RobertoPalozzo/esp32c3-case-design/Assessment_Files/200096469_RobertoPalozzo_ESP32Case_Final_Slicer.jpg

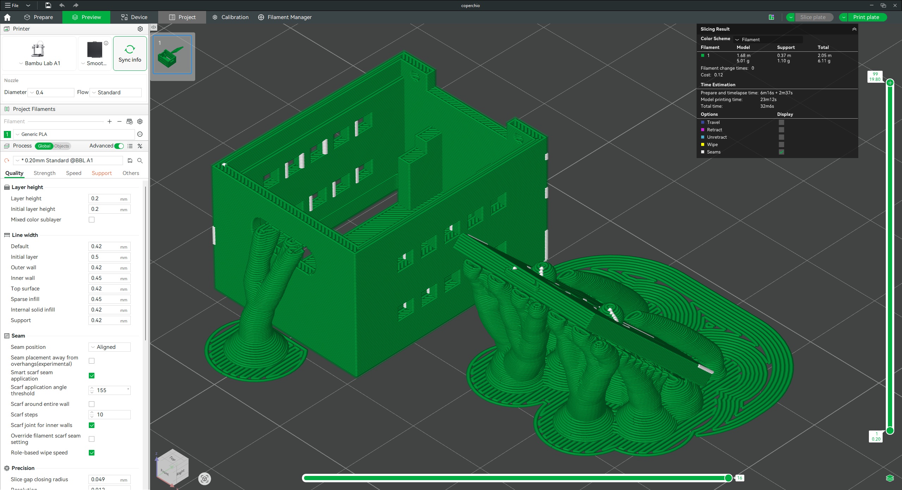
Assessment_Files/200096469_RobertoPalozzo_ESP32Case_Final_Slicer.jpg
