RobertoPalozzo/esp32c3-case-design/Assessment_Files/200096469_RobertoPalozzo_ESP32Case_Prototype1_Slicer.jpg

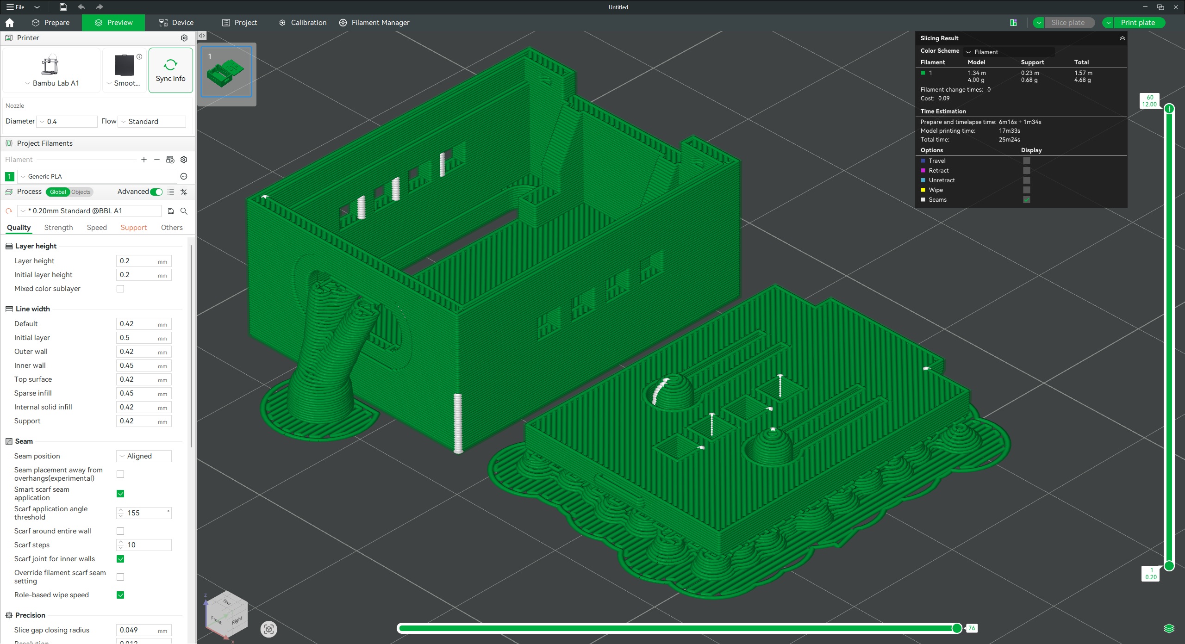
Assessment_Files/200096469_RobertoPalozzo_ESP32Case_Prototype1_Slicer.jpg
