RobertoPalozzo/esp32c3-case-design/images/alignment.jpg

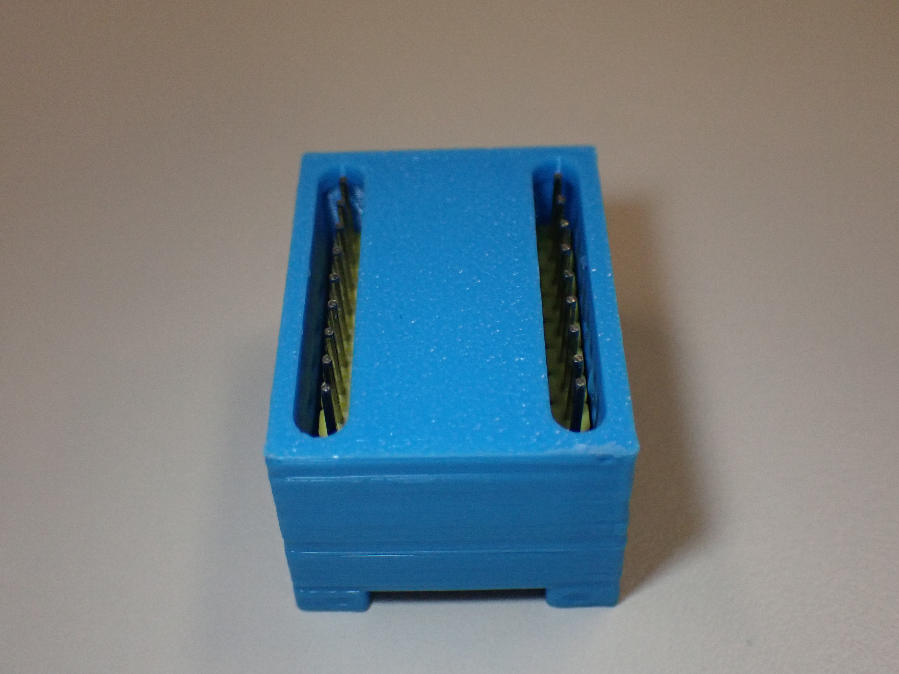
images/alignment.jpg
