RobertoPalozzo/esp32c3-case-design/images/board2.jpg

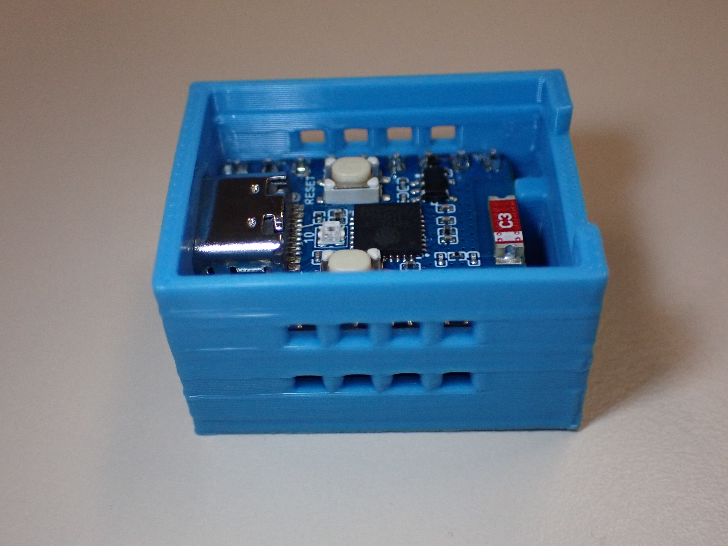
images/board2.jpg
