RobertoPalozzo/esp32c3-case-design/images/cable.jpg

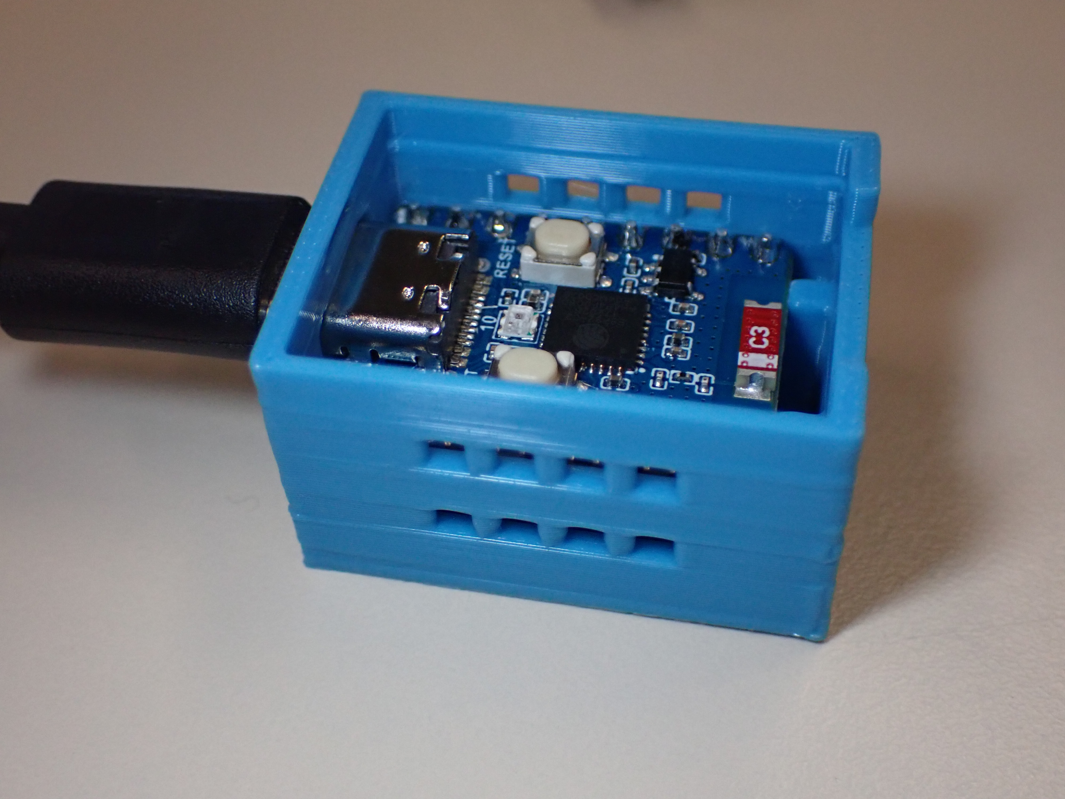
images/cable.jpg
