RobertoPalozzo/esp32c3-case-design/images/case1.jpg

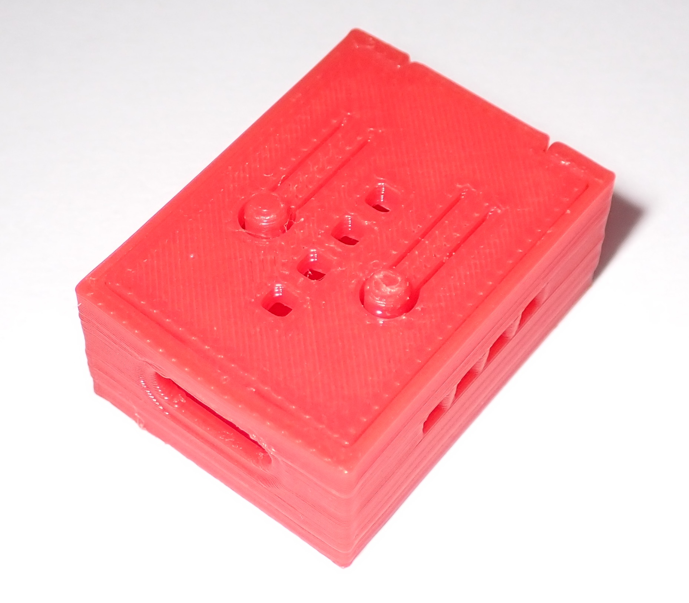
images/case1.jpg
