RobertoPalozzo/esp32c3-case-design/images/case2.jpg

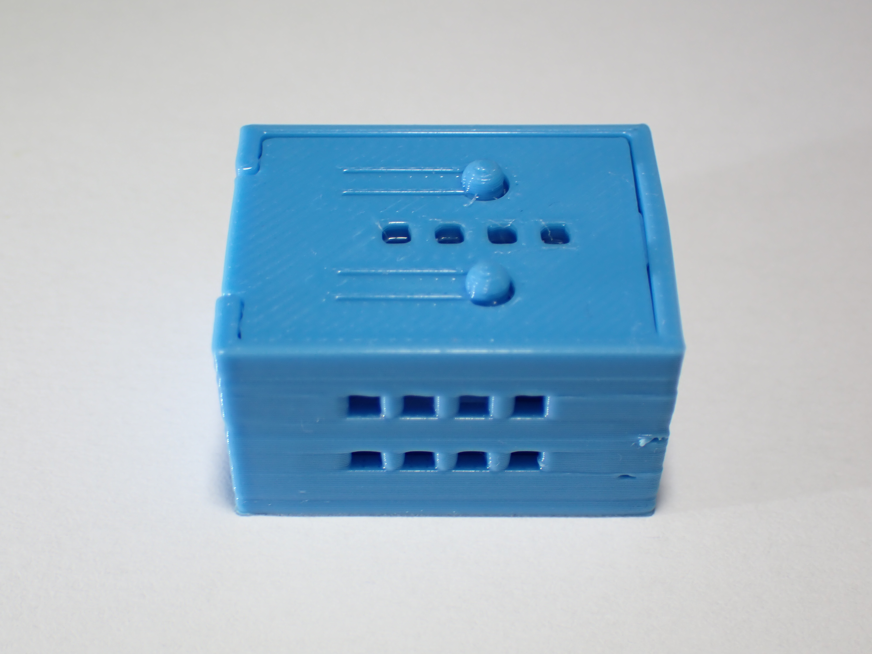
images/case2.jpg
