RobertoPalozzo/esp32c3-case-design/images/case3.jpg

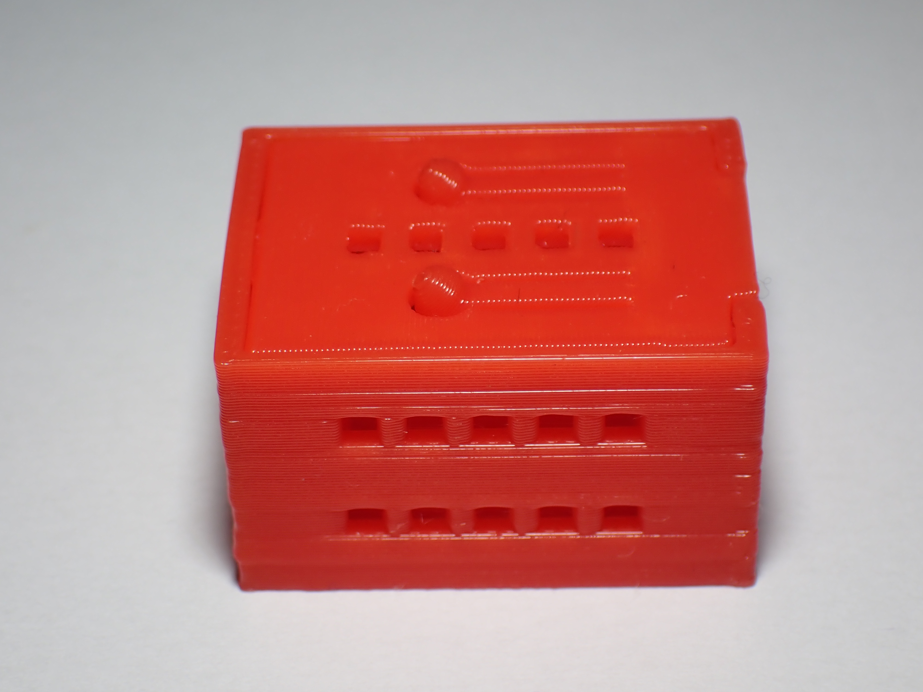
images/case3.jpg
