RobertoPalozzo/esp32c3-case-design/images/internal3.jpg

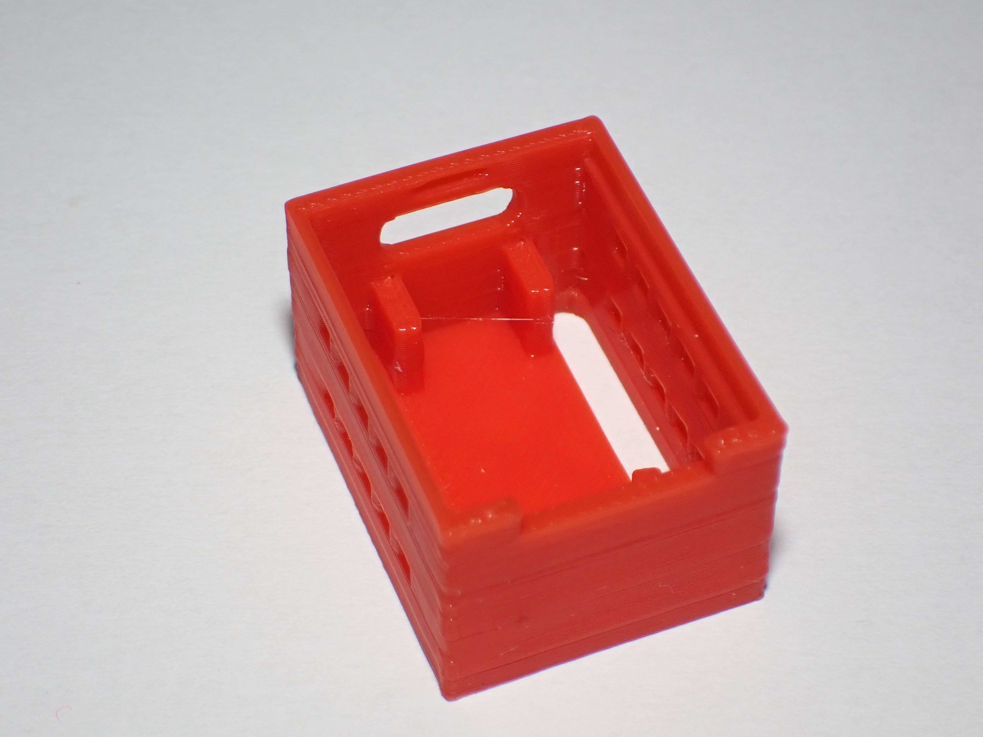
images/internal3.jpg
