RobertoPalozzo/esp32c3-case-design/images/Last_1_7.JPG

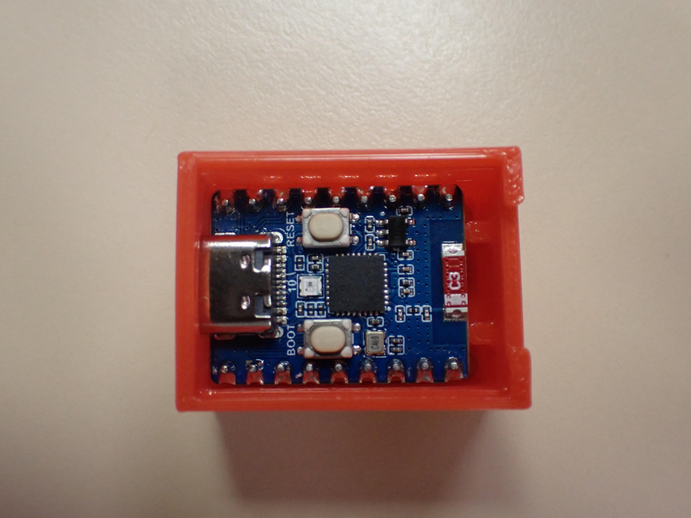
images/Last_1_7.JPG
