RobertoPalozzo/esp32c3-case-design/images/Last_1_9.JPG

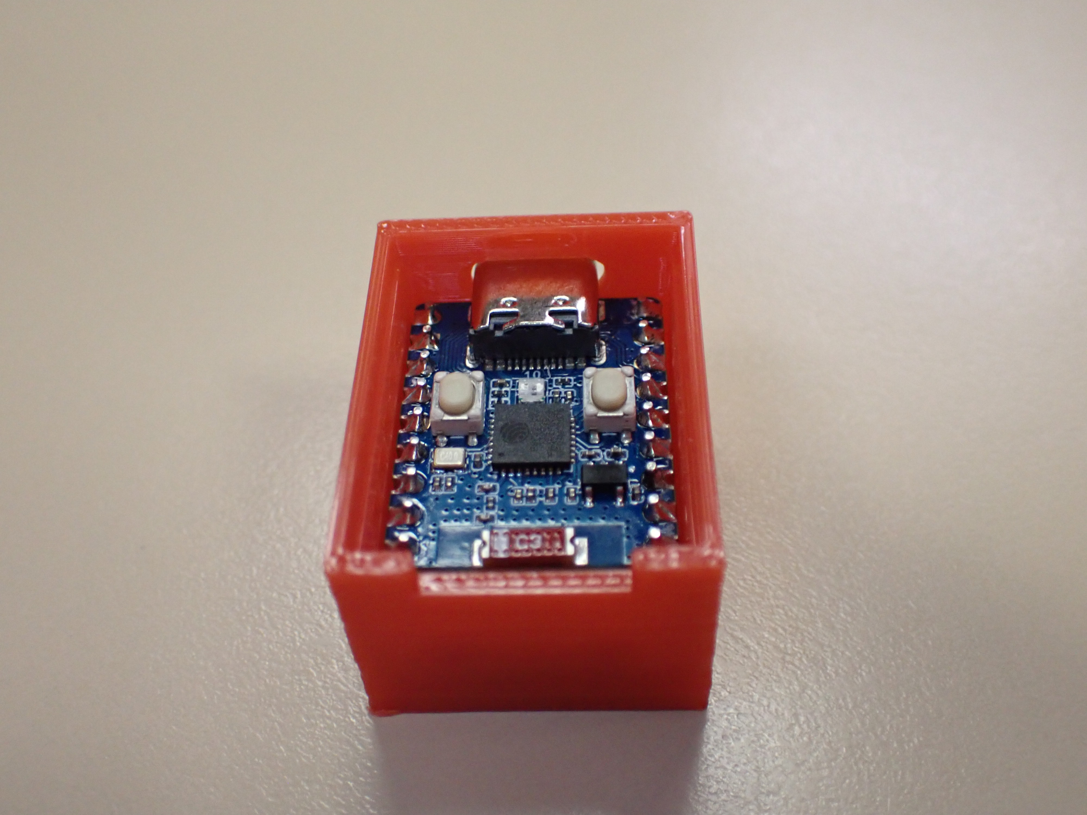
images/Last_1_9.JPG
