RobertoPalozzo/esp32c3-case-design/images/lid1.jpg

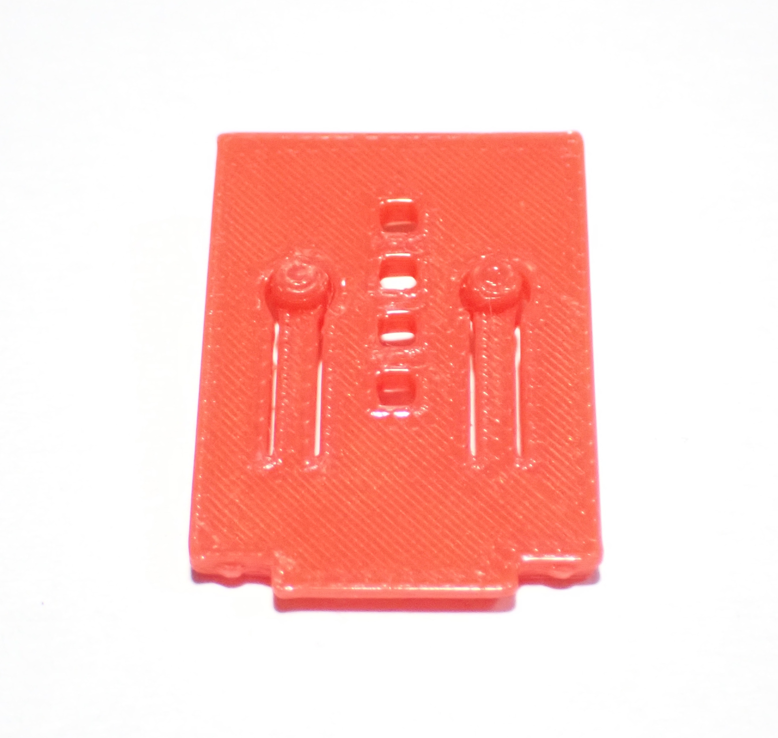
images/lid1.jpg
