RobertoPalozzo/esp32c3-case-design/images/lid3.jpg

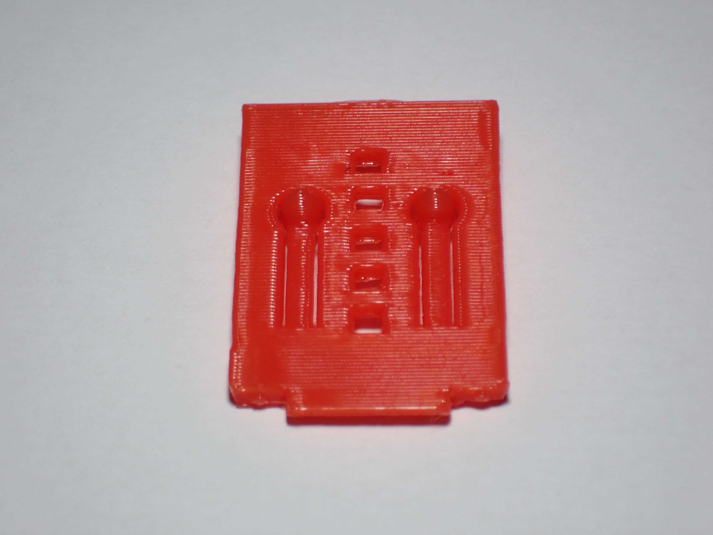
images/lid3.jpg
