RobertoPalozzo/esp32c3-case-design/images/long_pin.jpg

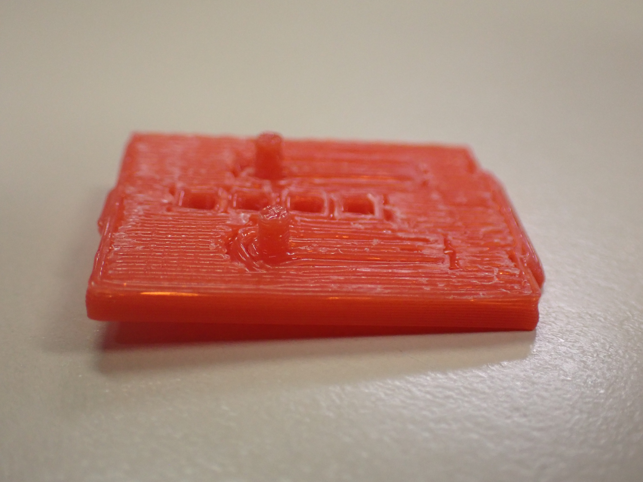
images/long_pin.jpg
