RobertoPalozzo/esp32c3-case-design/images/pins3.jpg

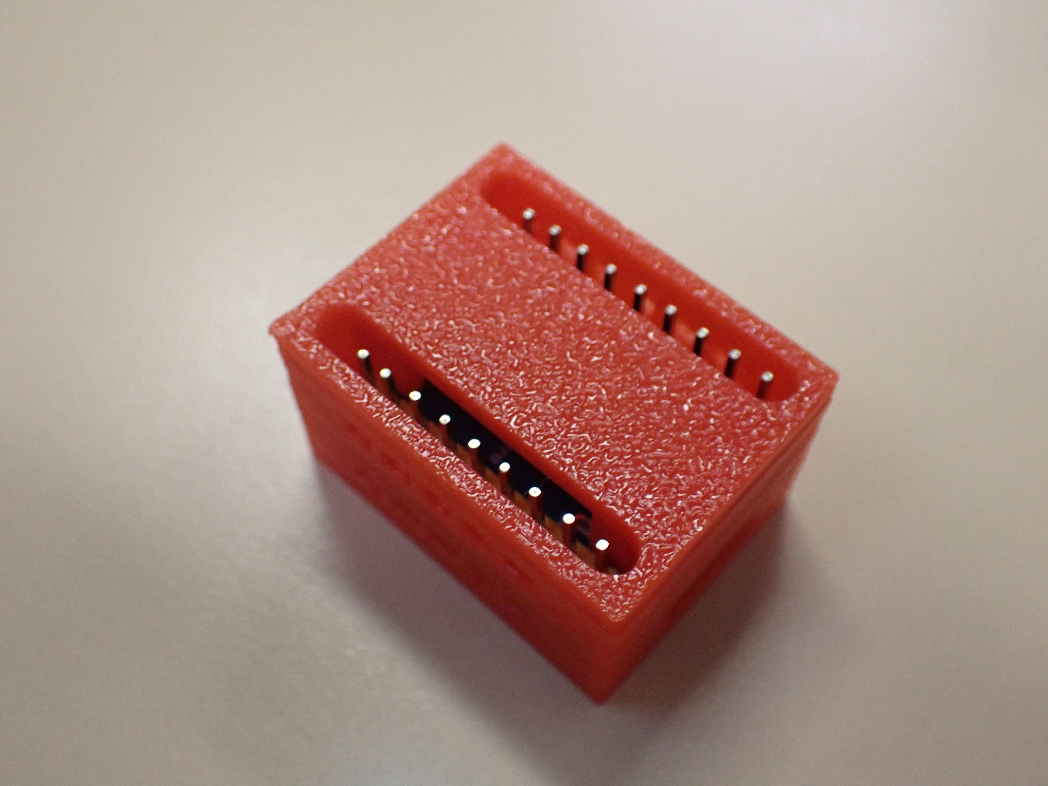
images/pins3.jpg
