RobertoPalozzo/esp32c3-case-design/images/prot1bot.jpg

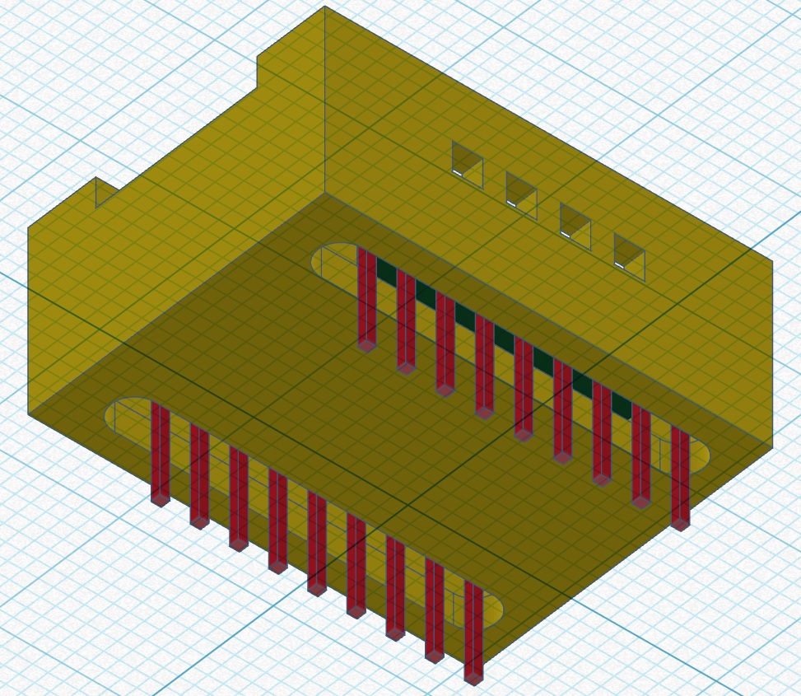
images/prot1bot.jpg
