RobertoPalozzo/esp32c3-case-design/images/prot1side3.jpg

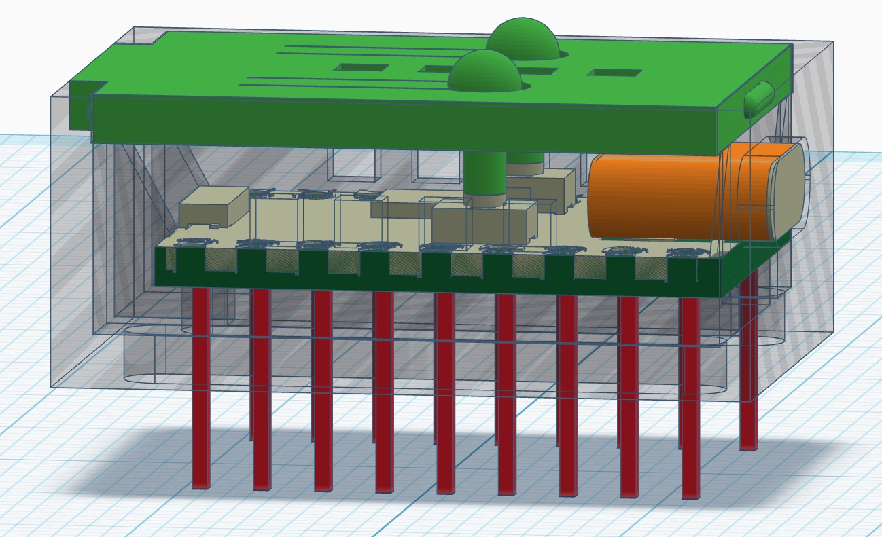
images/prot1side3.jpg
