RobertoPalozzo/esp32c3-case-design/images/prot1side.jpg

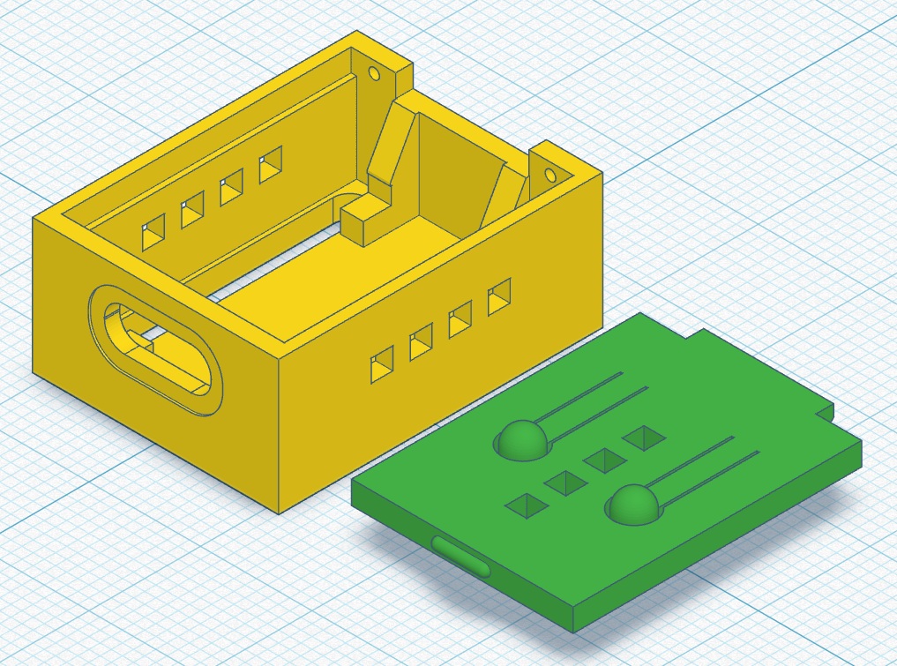
images/prot1side.jpg
