RobertoPalozzo/esp32c3-case-design/images/prot2bot.jpg

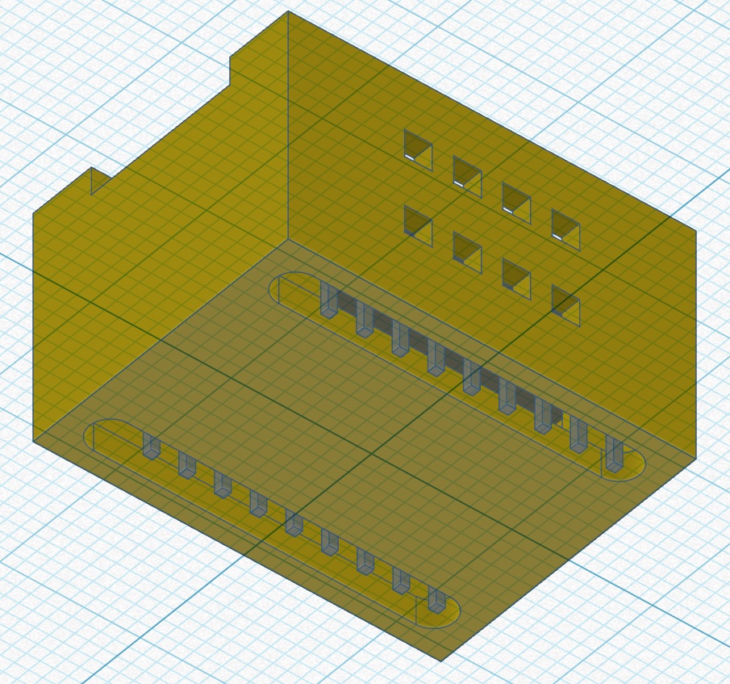
images/prot2bot.jpg
