RobertoPalozzo/esp32c3-case-design/images/prot2side.jpg

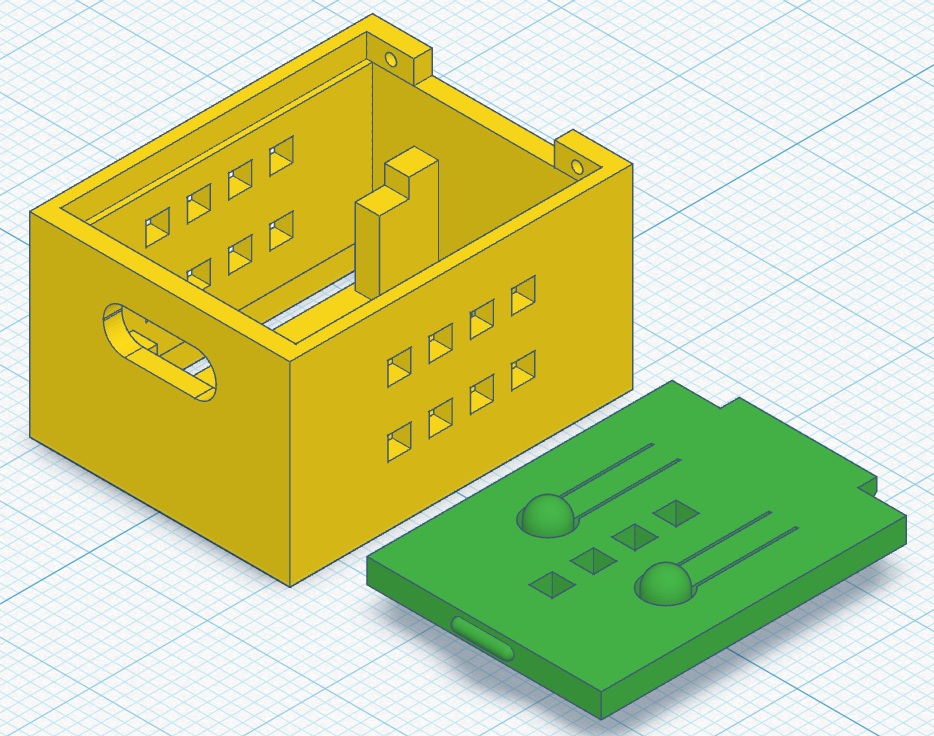
images/prot2side.jpg
