RobertoPalozzo/esp32c3-case-design/images/prot2up.jpg

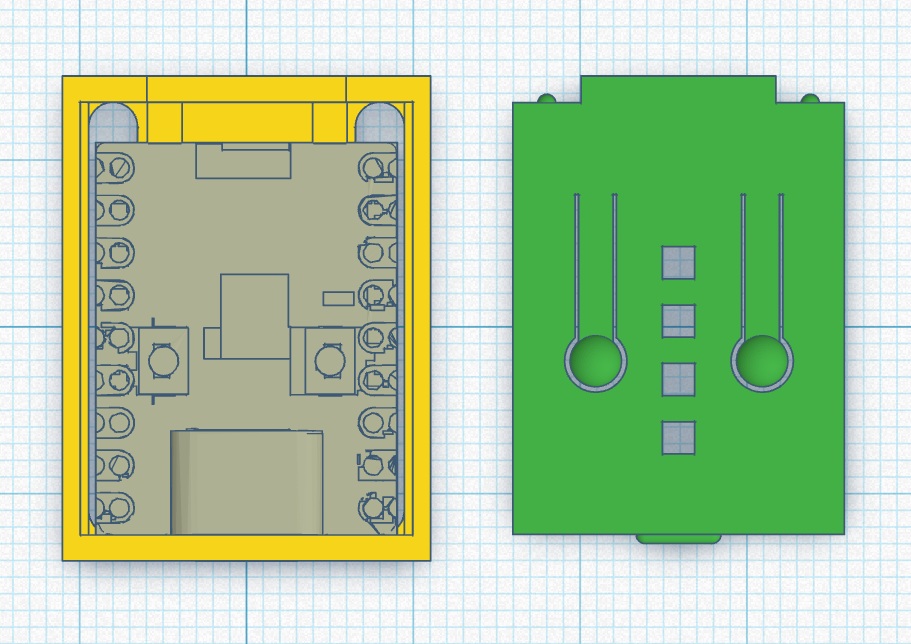
images/prot2up.jpg
