RobertoPalozzo/esp32c3-case-design/images/short_pins2.jpg

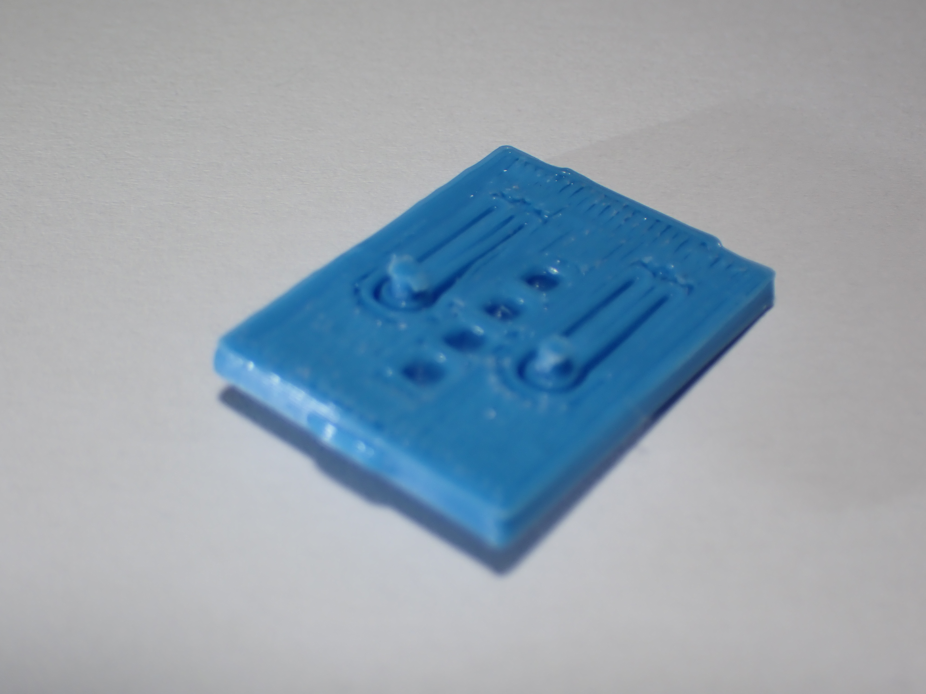
images/short_pins2.jpg
