RobertoPalozzo/esp32c3-case-design/images/slots2.jpg

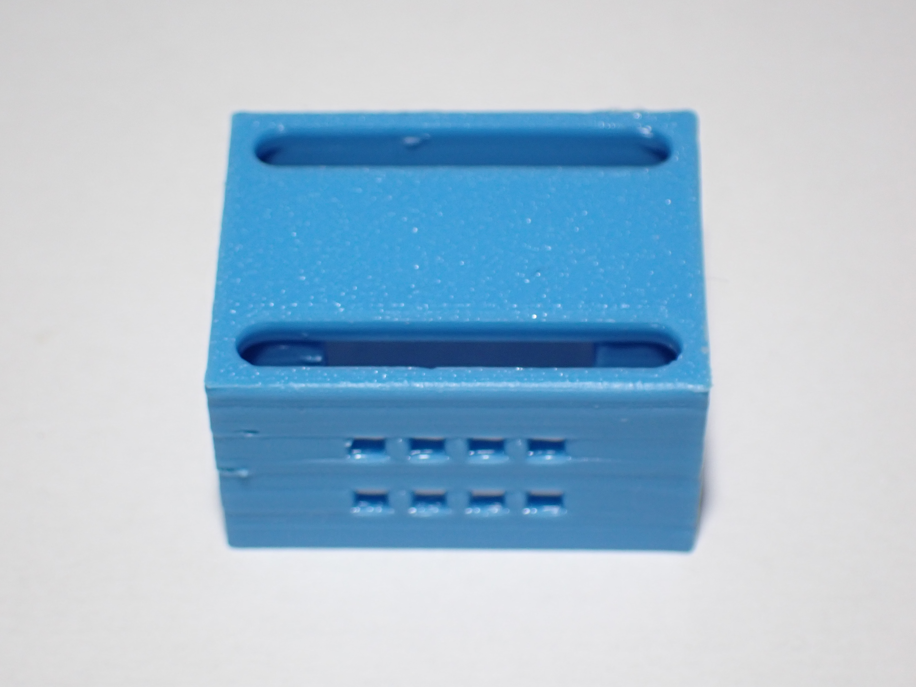
images/slots2.jpg
