RobertoPalozzo/esp32c3-case-design/images/space3.jpg

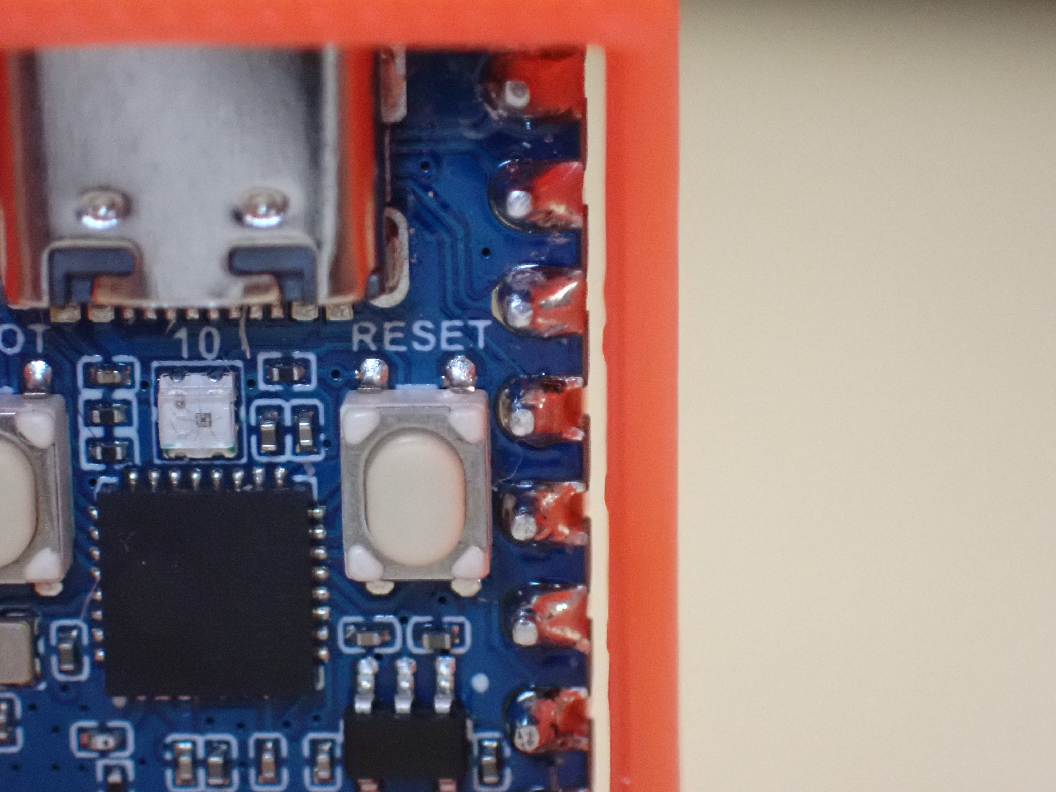
images/space3.jpg
