RobertoPalozzo/esp32c3-case-design/images/wall.jpg

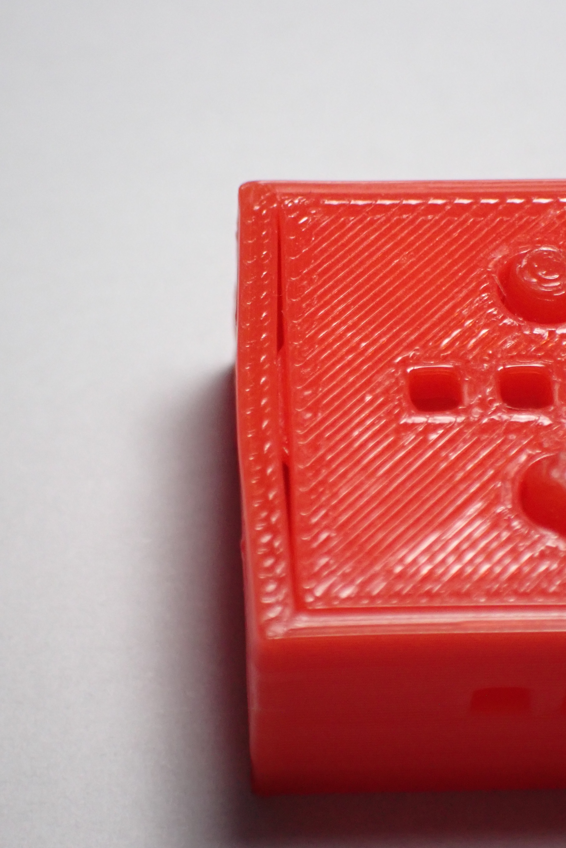
images/wall.jpg
